cristibaluta/Leica-G9ii/CADs/Base Plate-Threads.png

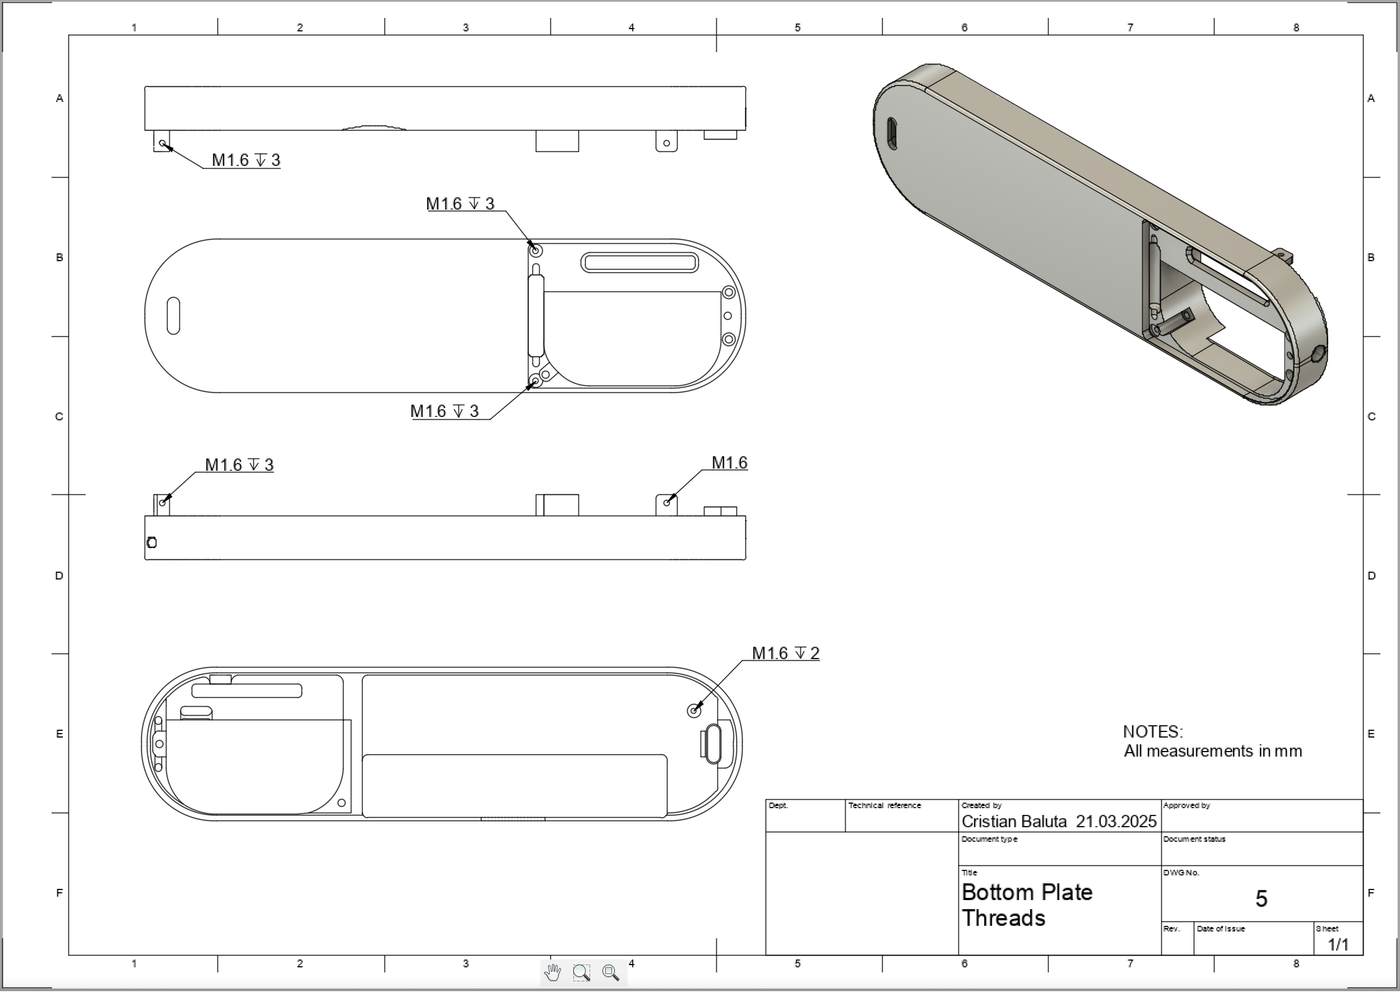
CADs/Base Plate-Threads.png
