cristibaluta/Leica-G9ii/CADs/Buttons-Threads.png

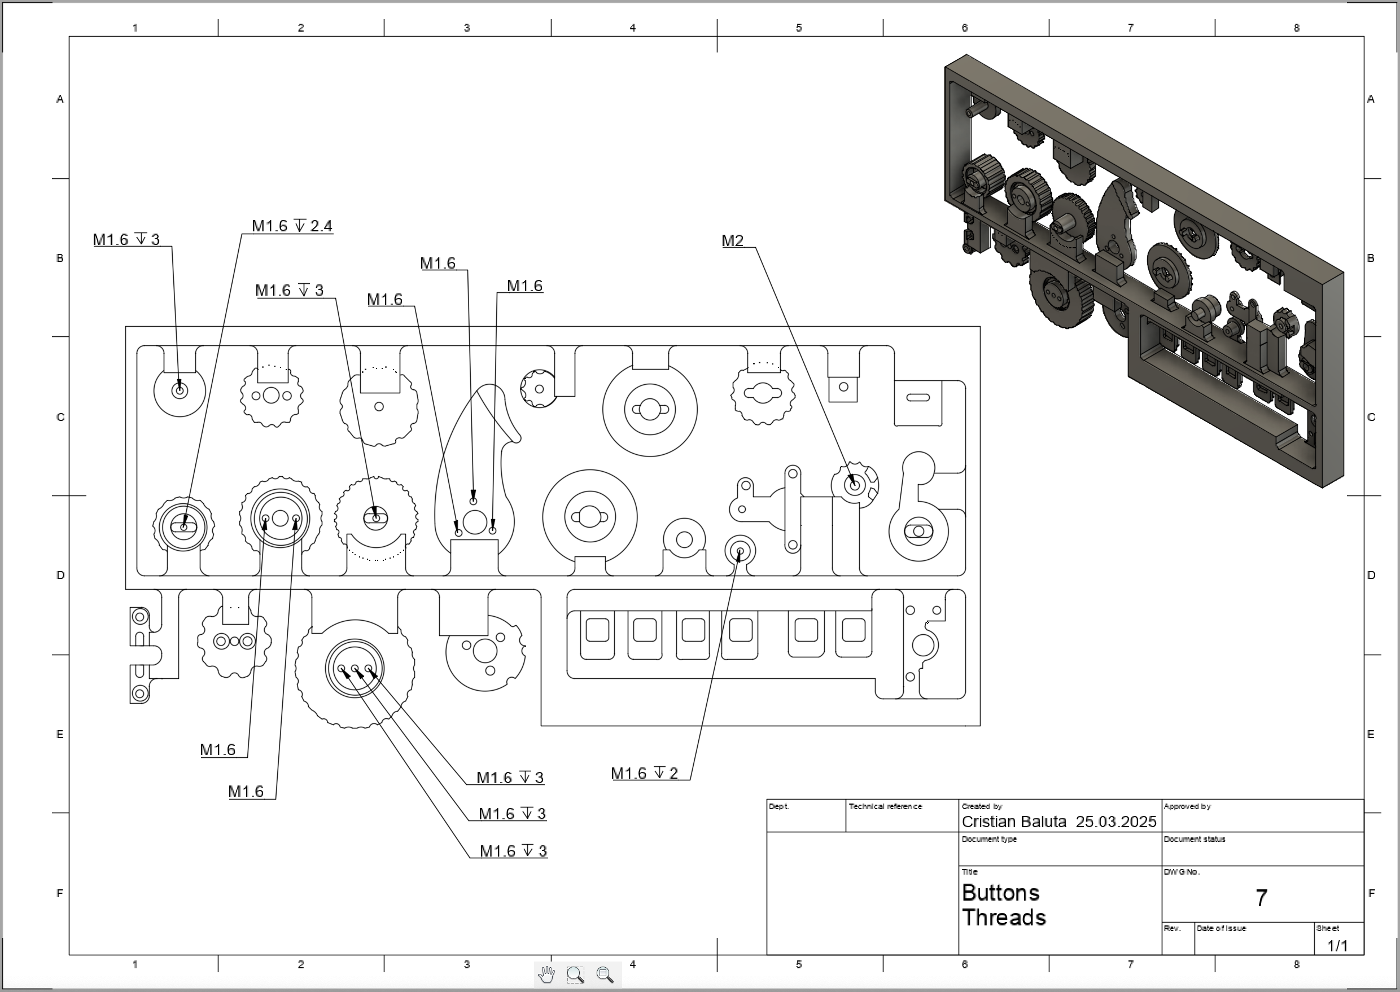
CADs/Buttons-Threads.png
