cristibaluta/Leica-G9ii/CADs/Dials/Levers-Threads.png

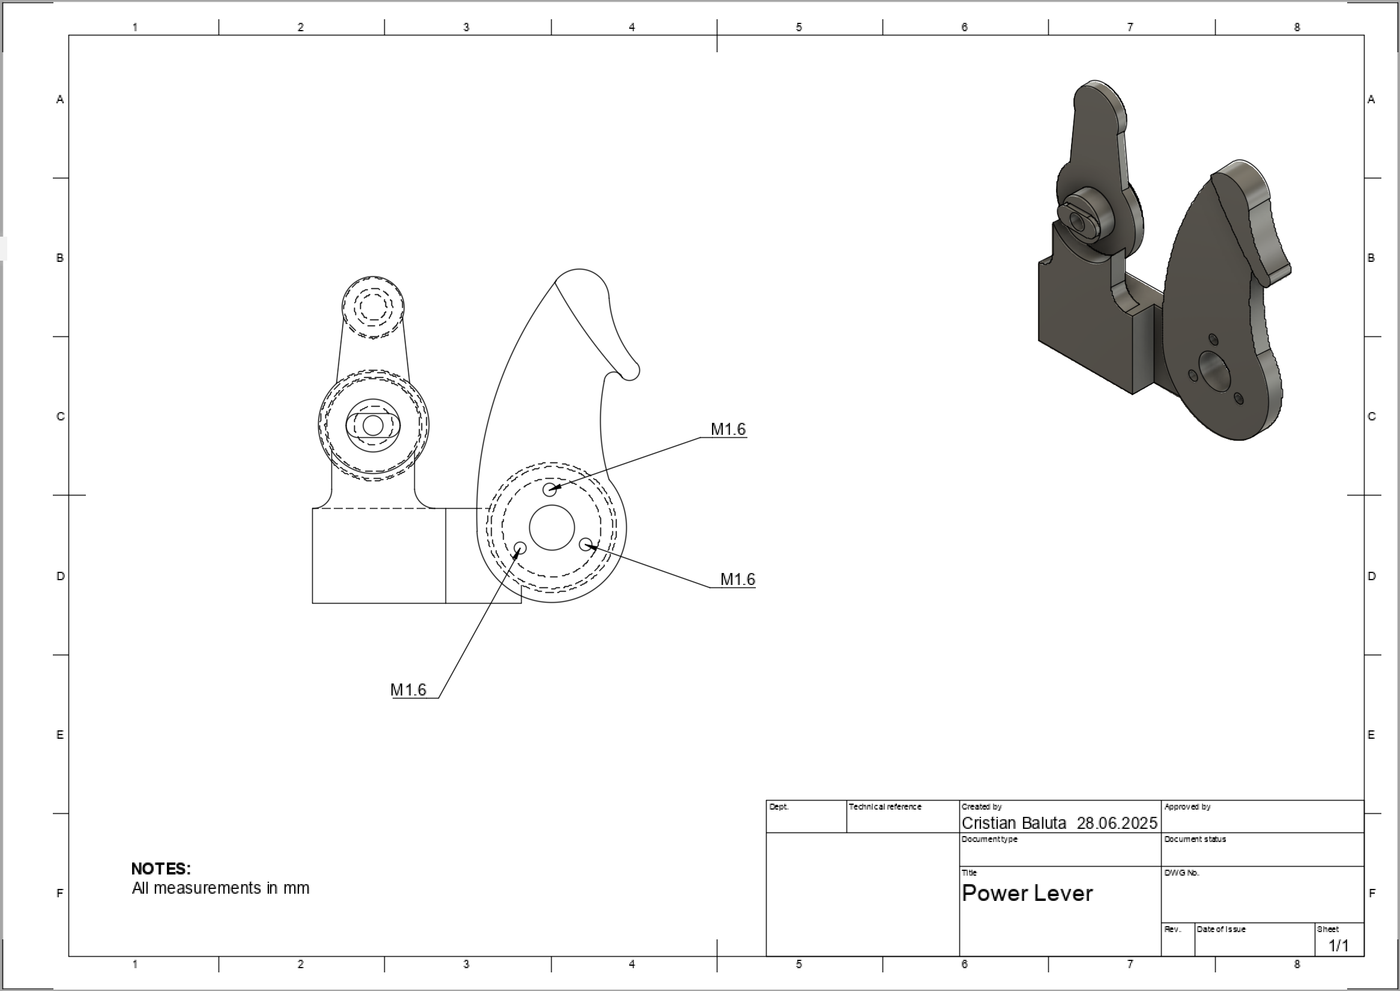
CADs/Dials/Levers-Threads.png
