cristibaluta/Leica-G9ii/CADs/Dials/Dials.step

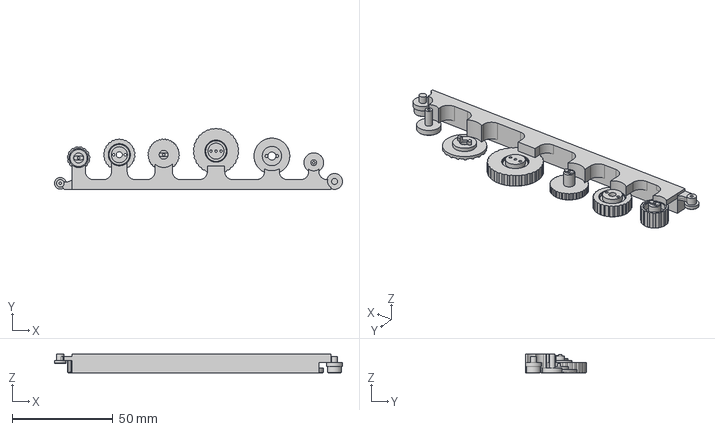
[picture p25: CAD file, 2025-06-29]
CADs/Dials/Dials.step
143.0 x 30.4 x 9.20 mm
