cristibaluta/Leica-G9ii/CADs/Dials/Levers.step

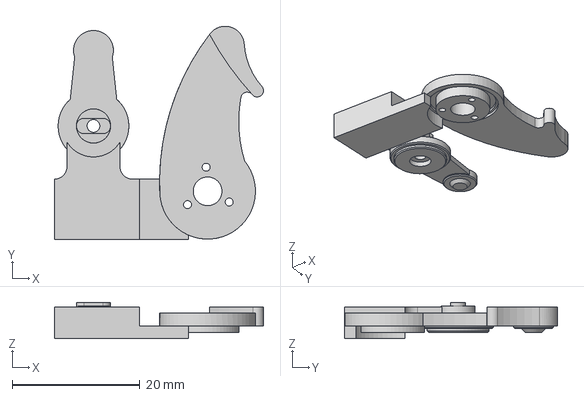
[picture p26: CAD file, 2025-06-29]
CADs/Dials/Levers.step
32.8 x 33.5 x 5.72 mm
