cristibaluta/Leica-G9ii/CADs/Dials/ModeDial.step

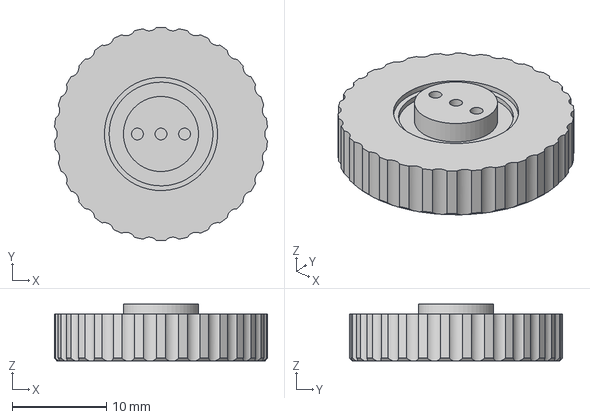
[picture p27: CAD file, 2025-06-09]
CADs/Dials/ModeDial.step
22.6 x 22.6 x 6.04 mm
